Elecrow-RD/CrowPanel-Advance-4.3-HMI-ESP32-S3-AI-Powered-IPS-Touch-Screen-800x480/example/V1.0/example_code4.3/lesson-07/README.md

# **The nRF2401 wireless module is used to receive and transmit signals** **example**

To complete this case, you need to refer to the detailed documentation tutorial, learn to connect to the gateway, and then burn code to send AT instructions. Detailed documentation tutorials can be found at the bottom of the page.

***\*Note: All examples run on ESP32 version 3.0.2.\****

### **How to use example**

Learn how to set up a gateway.After opening the sample code in the relevant code file with Arduino IDE.set the required configuration parameters and program it onto the development board

***\*Configuration parameter：\****

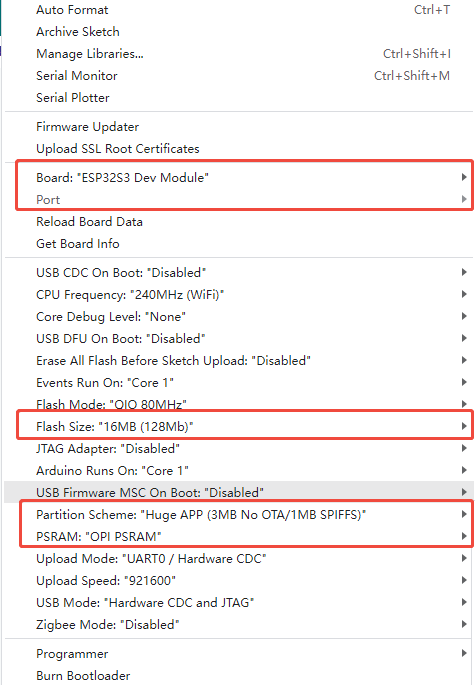
[picture p1: example/V1.0/example_code4.3/lesson-07/7-1.png]


**Note**:Before burning the code, be sure to set the switch on the back of the product to WM mode(0 1).

### **How to add Arduino libraries**

Replace the libraries file with the following path:

C:\Users\user name\Documents\Arduio\libraries

***\*Note\****: The 'user name' here is the same as the user computer account name.

## **Documentation tutorial link**：

https://www.elecrow.com/pub/wiki/7.Advance_wirelessmodule_lorawan.html

## **Video** **tutorial link**：
https://youtu.be/7SWwTssfDV8
