Elecrow-RD/CrowPanel-Advance-4.3-HMI-ESP32-S3-AI-Powered-IPS-Touch-Screen-800x480/example/V1.0/example_code4.3/lesson-05/README.md

# ****Connect to the sensor via the port to read temperature and humidity measurements example****

In this case, we connect the temperature and humidity sensor through the port to obtain the environmental temperature and humidity, and display the data on the Advanced AI screen in real time.

***\*Note: All examples run on ESP32 version 3.0.2.\****

### **How to use example**

After opening the sample code in the relevant code file with Arduino IDE.set the required configuration parameters and program it onto the development board

***\*Configuration parameter：\****

图片5-1

### **How to add Arduino libraries**

Replace the libraries file with the following path:

C:\Users\user name\Documents\Arduio\libraries

***\*Note\****: The 'user name' here is the same as the user computer account name.

## **Documentation tutorial link**：

https://www.elecrow.com/pub/wiki/4.3_5_Port_Introduction.html

## **Video** **tutorial link**：

https://www.youtube.com/watch?v=WM8ZcJ9OYKw&list=PLwh4PlcPx2Gfrtm7TmlARyF4ccTmIy-gK&index=5
