Elecrow-RD/CrowPanel-Advance-4.3-HMI-ESP32-S3-AI-Powered-IPS-Touch-Screen-800x480/example/V1.0/example_code4.3/lesson-06/README.md

# **The nRF2401 wireless module is used to receive and transmit signals** **example**

In this case, two nRF24L01 wireless modules are employed, with one module transmitting signals and the other receiving signals.

***\*Note: All examples run on ESP32 version 3.0.2.\****

### **How to use example**

After opening the sample code in the relevant code file with Arduino IDE.set the required configuration parameters and program it onto the development board

***\*Configuration parameter：\****



**Note**:Before burning the code, be sure to set the switch on the back of the product to WM mode(0 1).

### **How to add Arduino libraries**

Replace the libraries file with the following path:

C:\Users\user name\Documents\Arduio\libraries

***\*Note\****: The 'user name' here is the same as the user computer account name.

## **Documentation tutorial link**：

https://www.elecrow.com/pub/wiki/4.3_6_NRF2401_communication.html

## **Video** **tutorial link**：

https://www.youtube.com/watch?v=PHzW8t038Qo&list=PLwh4PlcPx2Gfrtm7TmlARyF4ccTmIy-gK&index=6
