Elecrow-RD/CrowPanel-Advance-4.3-HMI-ESP32-S3-AI-Powered-IPS-Touch-Screen-800x480/example/V1.1_and_V1.2_and_V1.3/IDF_Code/Lesson03-LVGL_Control_LED/components/lvgl__lvgl/demos/music/assets/png/480_png/btn_play.png

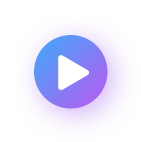
example/V1.1_and_V1.2_and_V1.3/IDF_Code/Lesson03-LVGL_Control_LED/components/lvgl__lvgl/demos/music/assets/png/480_png/btn_play.png
